Lessnullvoid/Pulsum-Plantae/pcb/pdfLM324Final/GalvanicoLM324Final_etch_mask_bottom.pdf

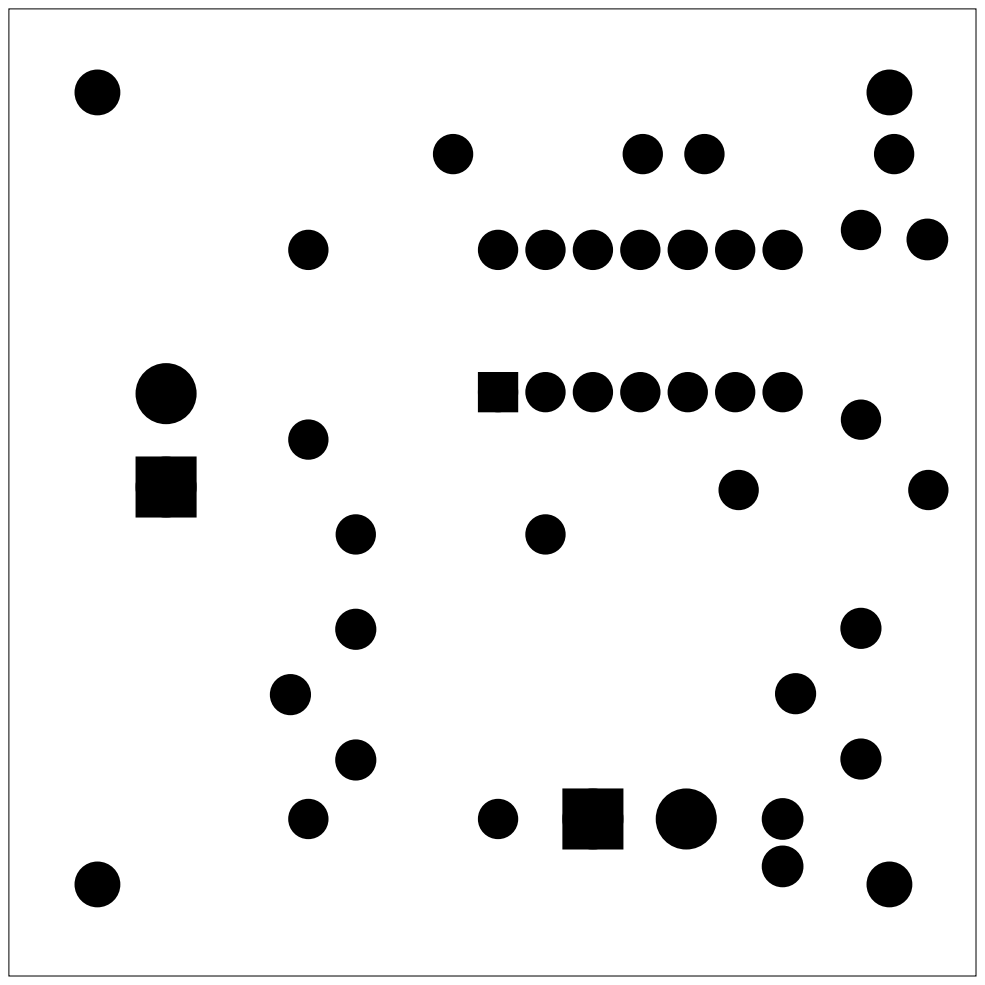
[picture p22: page 1]
