Lessnullvoid/Pulsum-Plantae/pcb/pdfLM324Final/GalvanicoLM324Final_etch_mask_bottom_mirror.pdf

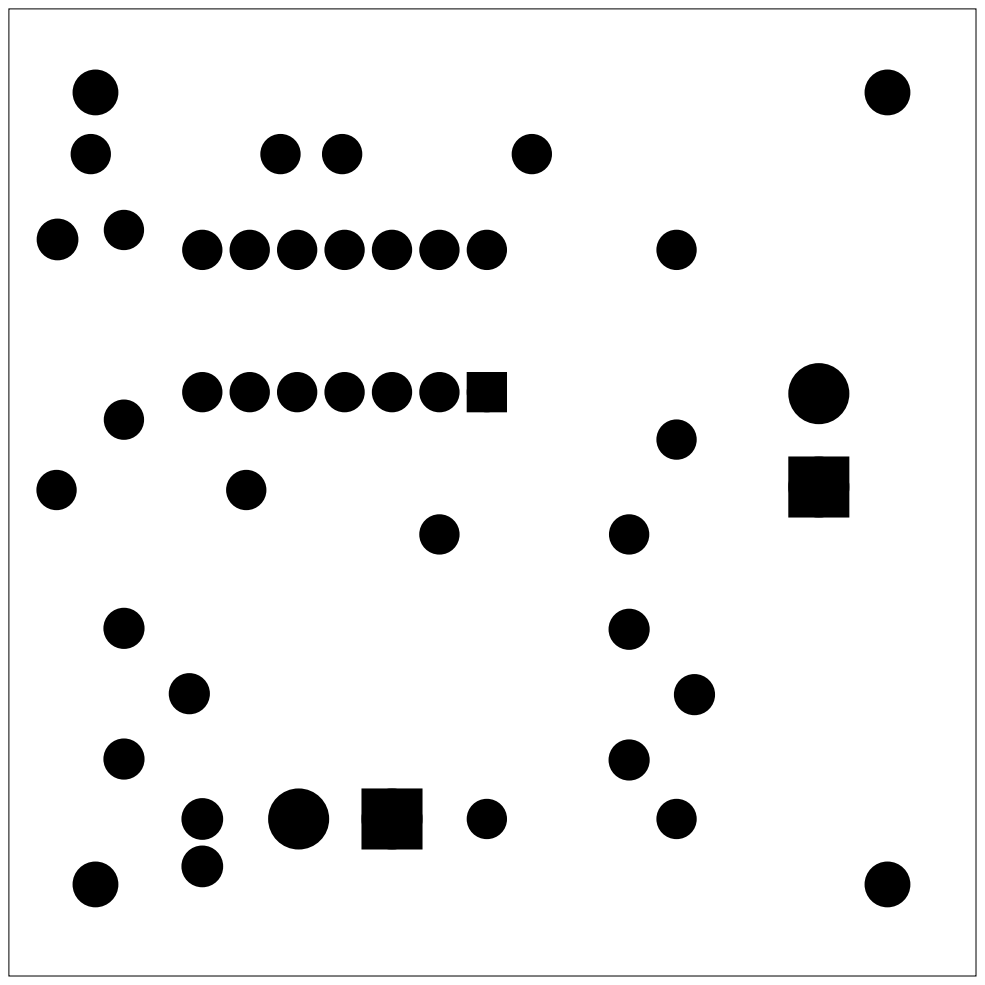
[picture p23: page 1]
