Lessnullvoid/Pulsum-Plantae/pcb/pdfLM324Final/GalvanicoLM324Final_etch_silk_bottom.pdf

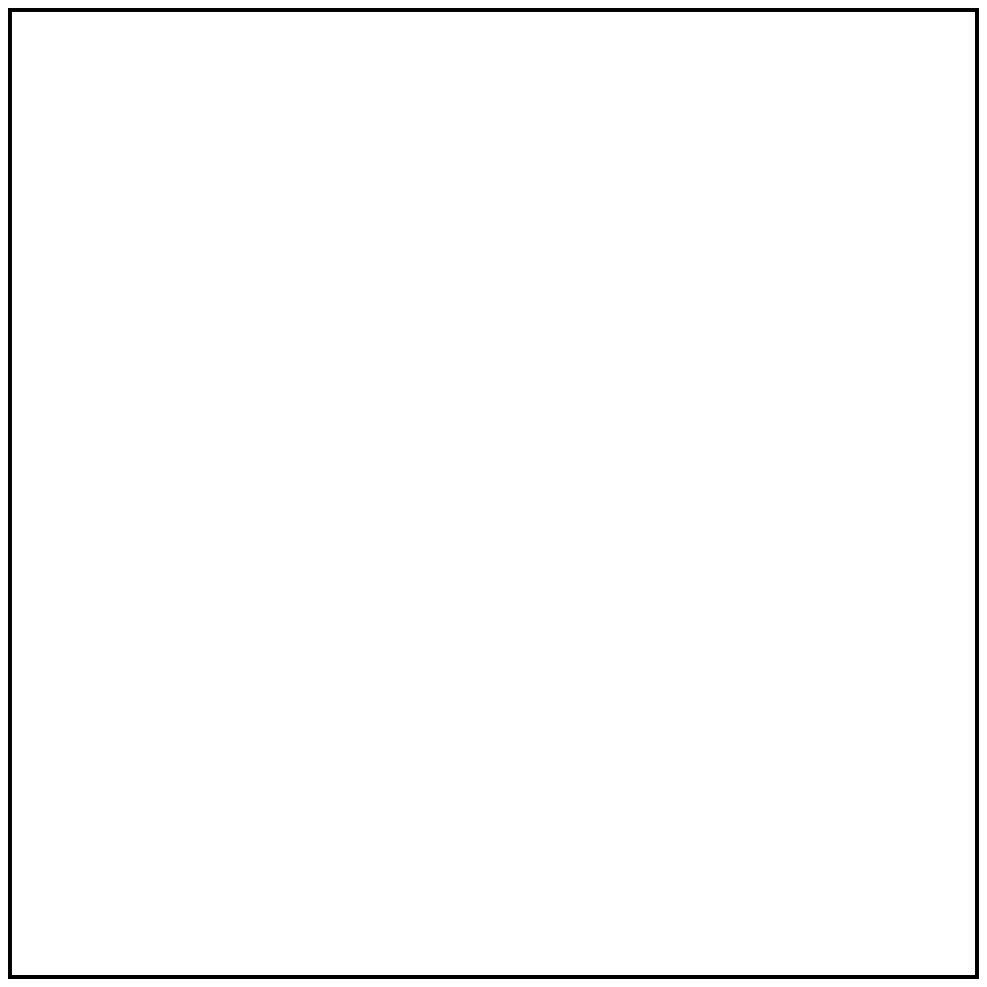
[picture p24: page 1]
