Lessnullvoid/Pulsum-Plantae/pcb/pdfLM324Final/GalvanicoLM324Final_etch_silk_bottom_mirror.pdf

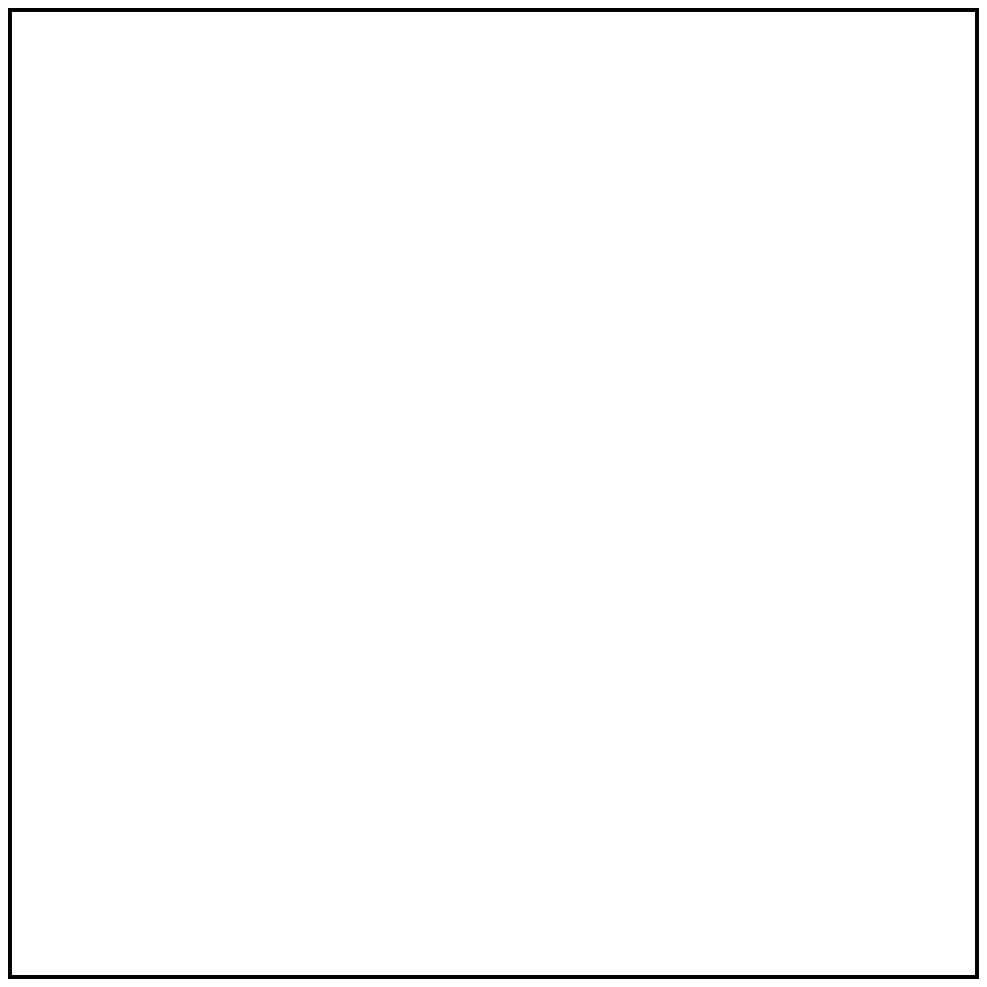
[picture p25: page 1]
