Lessnullvoid/Pulsum-Plantae/pcb/pdfLM324Final/GalvanicoLM324Final_etch_silk_top.pdf

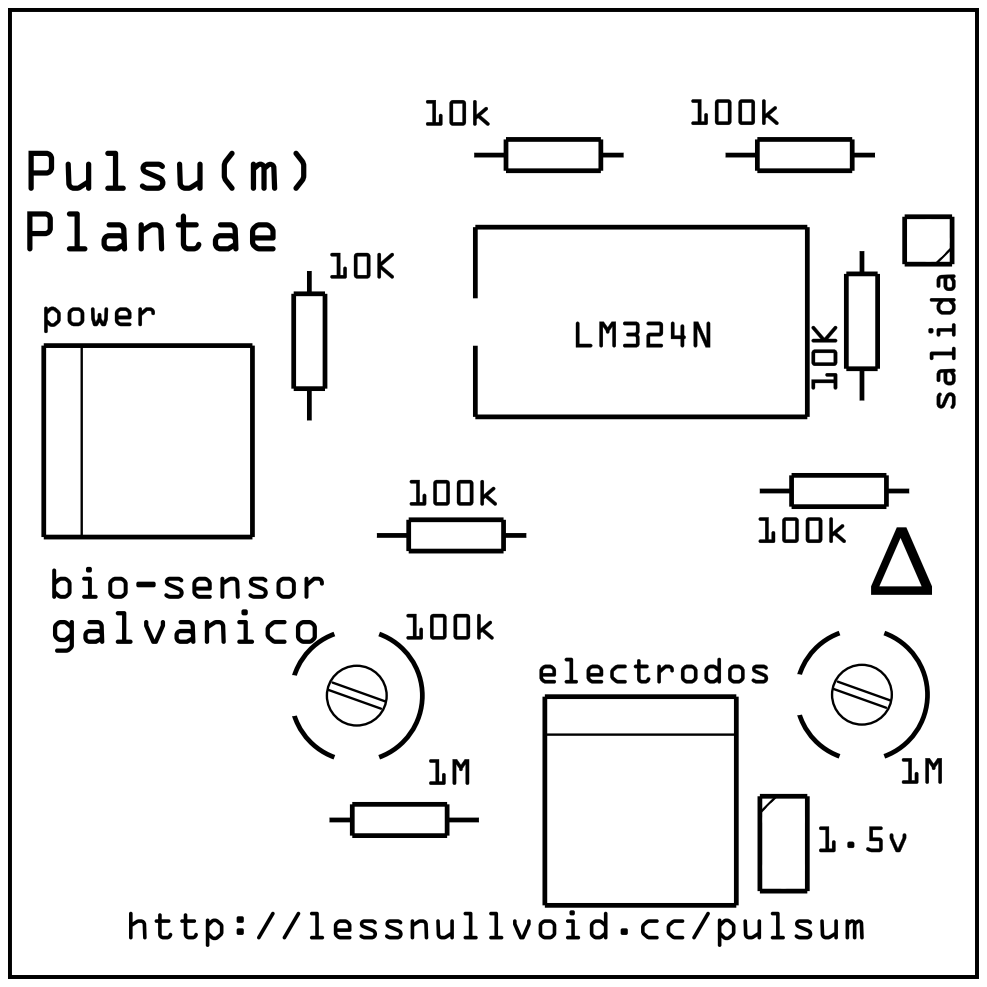
[picture p26: page 1]
