Lessnullvoid/Pulsum-Plantae/pcb/pdfLM324Final/GalvanicoLM324Final_etch_silk_top_mirror.pdf

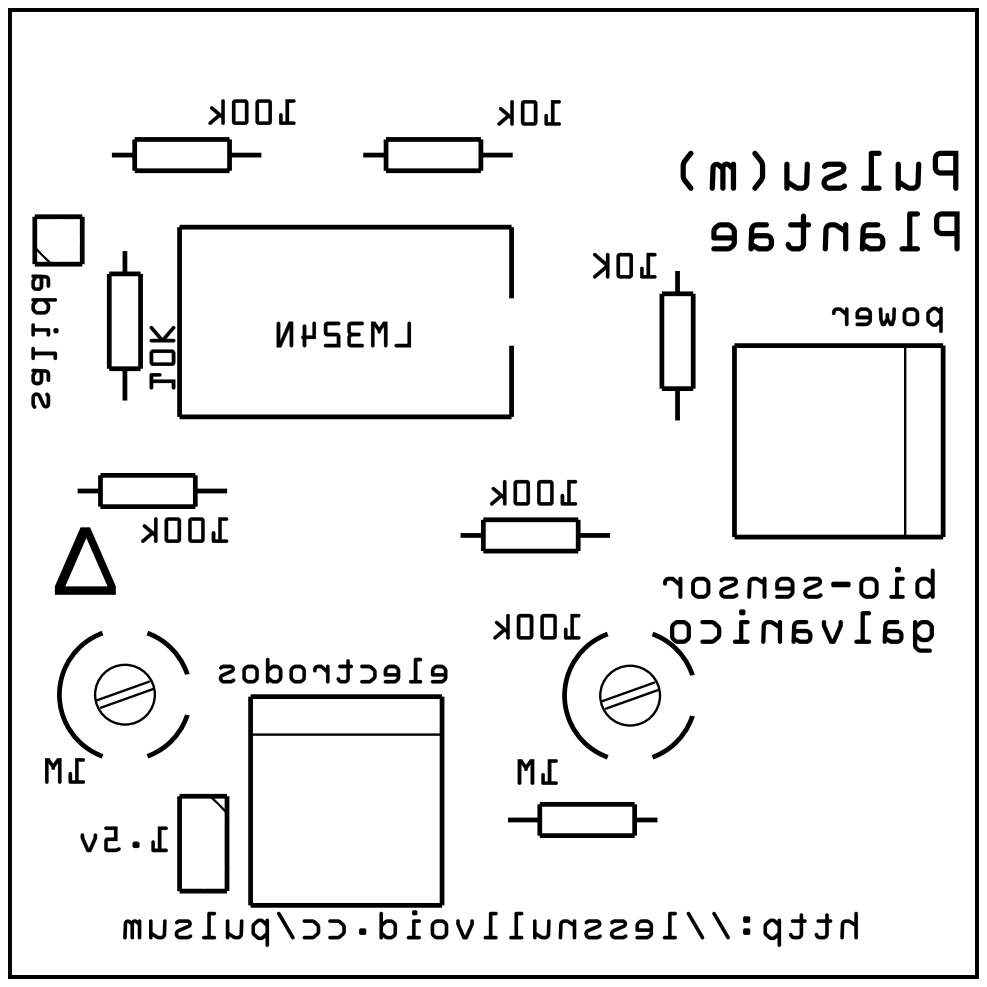
[picture p27: page 1]
