Lessnullvoid/Pulsum-Plantae/pcb/358PDF/Galvanico358_etch_copper_bottom_mirror.pdf

### Biosensor

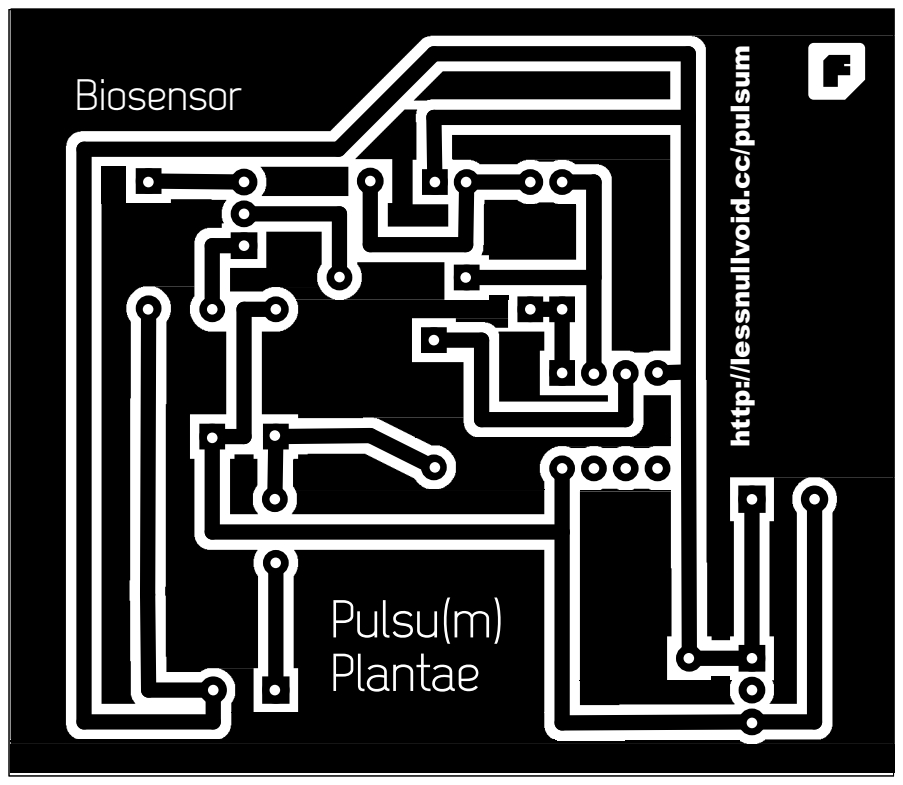
[picture p28: page 1]
Pulsu(m) Plantae

http://lessnullvoid.cc/pulsum
