Lessnullvoid/Pulsum-Plantae/pcb/lm324nPDF/GalvanicoLM324n_etch_copper_bottom_mirror.pdf

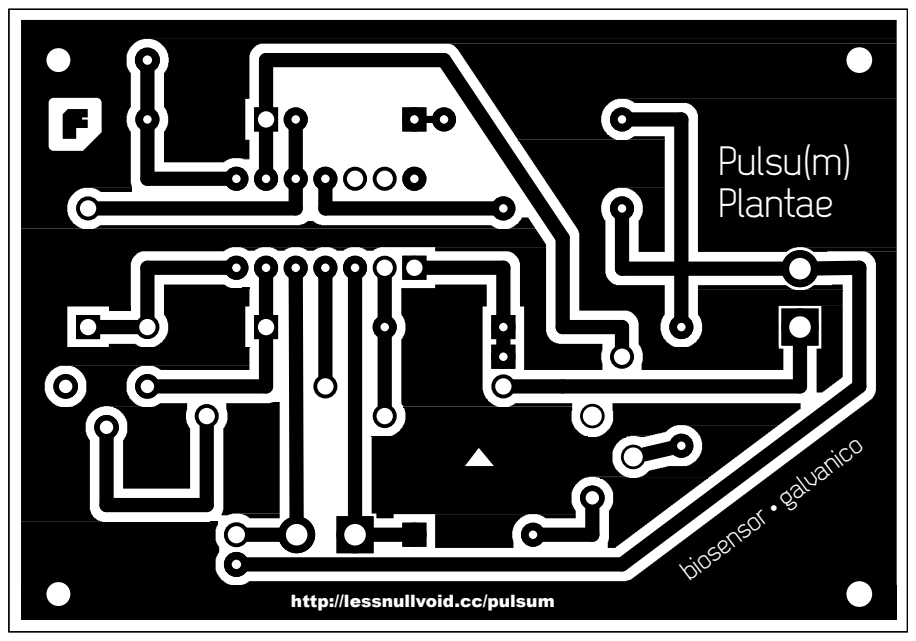
[picture p29: page 1]
Pulsu(m) Plantae; biosensor • galvanico

http://lessnullvoid.cc/pulsum
