Lessnullvoid/Pulsum-Plantae/pcb/lm324nPDF/GalvanicoLM324n_etch_silk_top_mirror.pdf

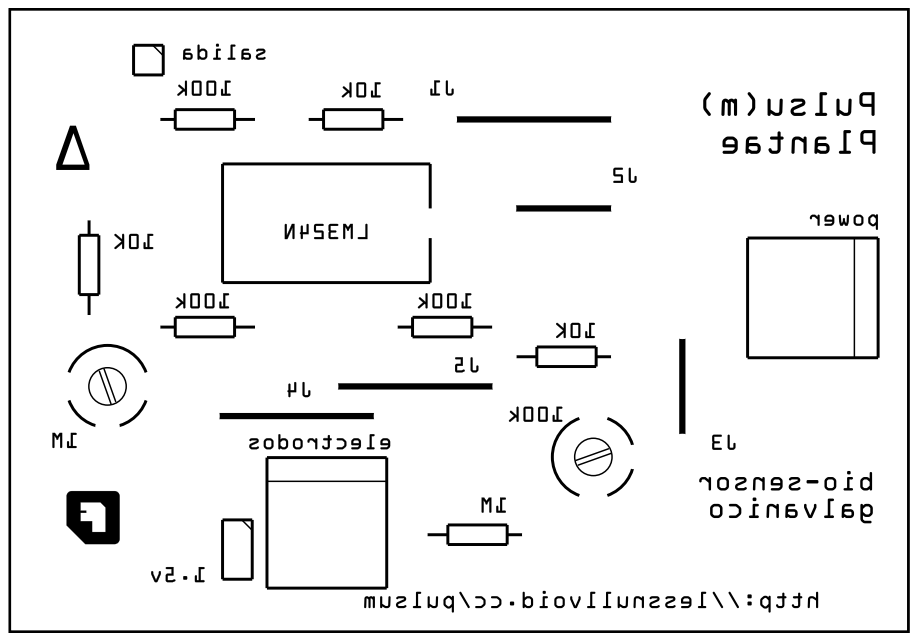
[picture p30: page 1]
